AvisOfTheStars/BAE305-SP25-Pinball/FullCode/Ben_Code_4_30_25_copy_20250430222031/Ben_Code_4_30_25_copy_20250430222031.ino

#include <LiquidCrystal.h>

// LCD wiring: RS=D12, E=D11, D4=D10, D5=D9, D6=D8, D7=D7
LiquidCrystal lcd(12, 11, 10, 9, 8, 7);

// Pin Assignments
const int leftFlipperPin = 2;
const int rightFlipperPin = 3;
const int leftButtonPin = 4;
const int rightButtonPin = 6;
const int resetButtonPin = 5;
const int piezoPin = 1; // D1 (RX) — Serial disabled

// Scoring Sensors
const int scorePins[] = {A1, A2, A3, A4};
const int numScorePins = sizeof(scorePins) / sizeof(scorePins[0]);
int scoreThresholds[] = {400, 800, 500, 800}; // Individual thresholds

// Game Over Sensor
const int gameOverSensorPin = A5;
int gameOverThreshold = 450;  // Lowered from 750 to prevent boot trigger

// Game Logic
int score = 0;
bool gameOver = false;
unsigned long lastBounceTime = 0;
const int debounceDelay = 200;

void setup() {
  // LCD init
  lcd.begin(16, 2);
  lcd.setCursor(0, 0);
  lcd.print("Pinball Machine");
  lcd.setCursor(0, 1);
  lcd.print("Score: 0");

  // Flippers
  pinMode(leftFlipperPin, OUTPUT);
  pinMode(rightFlipperPin, OUTPUT);
  digitalWrite(leftFlipperPin, HIGH);
  digitalWrite(rightFlipperPin, HIGH);

  // Buttons
  pinMode(leftButtonPin, INPUT_PULLUP);
  pinMode(rightButtonPin, INPUT_PULLUP);
  pinMode(resetButtonPin, INPUT_PULLUP);

  // Score sensors
  for (int i = 0; i < numScorePins; i++) {
    pinMode(scorePins[i], INPUT);
  }

  // Game over sensor
  pinMode(gameOverSensorPin, INPUT);

  // Sensor Calibrartion
  for (int j = 0; j < numScorePins; j++) {
    scoreThresholds[j] = calibrate(scorePins[j]);
  }
  gameOverThreshold = calibrate(gameOverSensorPin);
}

void loop() {
  handleFlippers(); // Always allow flipper control

  if (!gameOver) {
    handleScoring();
    checkGameOverSensor();
  } else {
    handleReset();
  }
}

void handleScoring() {
  for (int i = 0; i < numScorePins; i++) {
    int sensorValue = analogRead(scorePins[i]);

    if (sensorValue < scoreThresholds[i] && (millis() - lastBounceTime > debounceDelay)) {
      score += 10;
      lastBounceTime = millis();
      updateDisplay();
      playCoinSound(); // D1 piezo buzz
    }
  }
}

void handleFlippers() {
  digitalWrite(leftFlipperPin, (digitalRead(leftButtonPin) == LOW) ? LOW : HIGH);
  digitalWrite(rightFlipperPin, (digitalRead(rightButtonPin) == LOW) ? LOW : HIGH);
}

void checkGameOverSensor() {
  int gameOverValue = analogRead(gameOverSensorPin);

  if (gameOverValue < gameOverThreshold) {
    gameOver = true;
    lcd.clear();
    lcd.setCursor(0, 0);
    lcd.print("Game Over");
    lcd.setCursor(0, 1);
    lcd.print("Press Reset Btn");
  }
}

void handleReset() {
  if (digitalRead(resetButtonPin) == LOW) {
    delay(200); // debounce
    analogRead(gameOverSensorPin); // Test to see if value is sticking in memory
    score = 0;
    gameOver = false;
    updateDisplay();
  }
}

void playCoinSound() {
  tone(piezoPin, 1318, 80); // E6
  delay(90);
  tone(piezoPin, 1568, 80); // G6
  delay(90);
  tone(piezoPin, 1760, 80); // A6
  delay(90);
  noTone(piezoPin);
}

void updateDisplay() {
  lcd.clear();
  lcd.setCursor(0, 0);
  lcd.print("Pinball Machine");
  lcd.setCursor(0, 1);
  lcd.print("Score: ");
  lcd.print(score);
}

int calibrate(int pin) {
  int calibTotal = 0;
  int i = 0;
  for (i = 0; i < 5000; i++) {
    calibTotal += analogRead(pin);
  }
  int sensorLimit = (calibTotal / i);
  return (sensorLimit - 50);
}
