AvisOfTheStars/BAE305-SP25-Pinball/LCDCode.ino

/*
  SparkFun Inventor’s Kit
  Circuit 4A-HelloWorld

  The LCD will display the words "Hello World" and show how many seconds have passed since
  the RedBoard was last reset.

  This sketch was written by SparkFun Electronics, with lots of help from the Arduino community.
  This code is completely free for any use.

  View circuit diagram and instructions at: https://learn.sparkfun.com/tutorials/sparkfun-inventors-kit-experiment-guide---v41
  Download drawings and code at: https://github.com/sparkfun/SIK-Guide-Code
*/
int position = 0;
#include <LiquidCrystal.h>          //the liquid crystal library contains commands for printing to the display

LiquidCrystal lcd(13, 12, 11, 10, 9, 8);   // tell the RedBoard what pins are connected to the display

void setup() {
  
  lcd.begin(16, 2);                 //tell the lcd library that we are using a display that is 16 characters wide and 2 characters high
 lcd.setCursor(position, 0);
  lcd.print("Hello, world!");
}

void loop() {
  lcd.setCursor(position, 0);
  lcd.print("Hello, world!");
  lcd
  lcd.noDisplay();
  delay(300);
  lcd.display();
  position--;
  delay(150);
}
